TinyCircuits/TinyCircuits-Wireling-Temperature-Sensor-AST1021/cad/Wireling_TEMP_AST1021_REV2-DETAILED_DRAWING-PNG.png

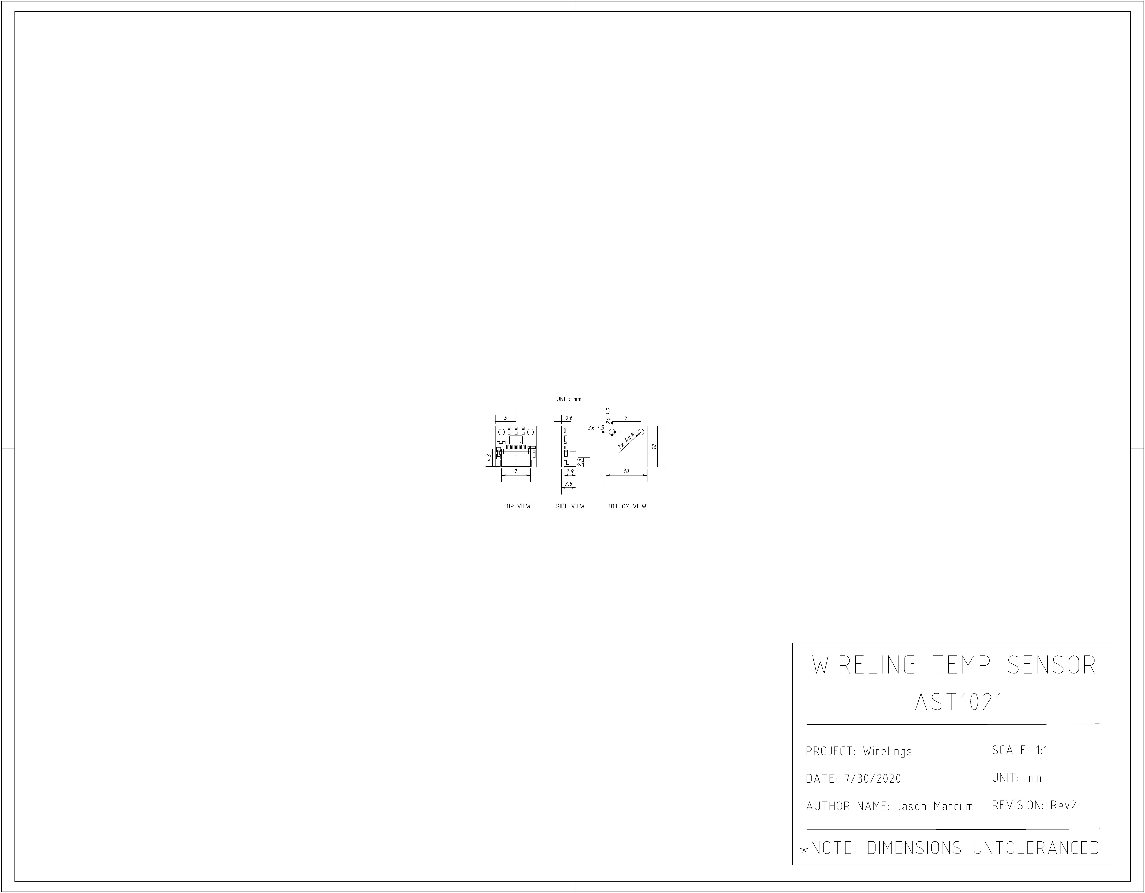
cad/Wireling_TEMP_AST1021_REV2-DETAILED_DRAWING-PNG.png
