TinyCircuits/TinyCircuits-Wireling-Temperature-Sensor-AST1021/images/AST1021-Product-Photo-01.png

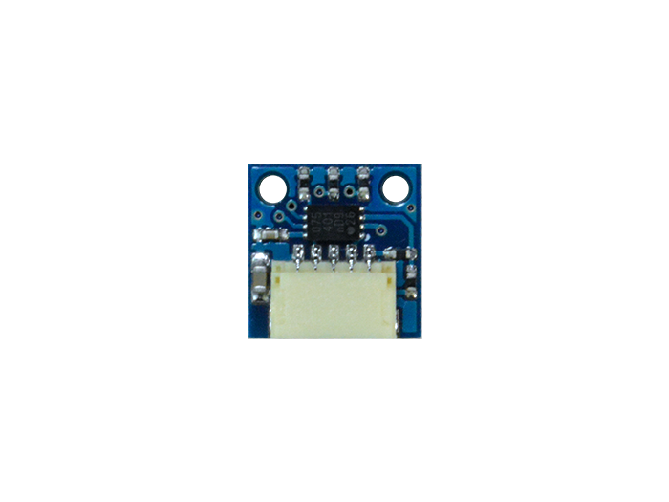
images/AST1021-Product-Photo-01.png
