TinyCircuits/TinyCircuits-Wireling-Temperature-Sensor-AST1021/images/AST1021-Tutorial-Image-03.gif

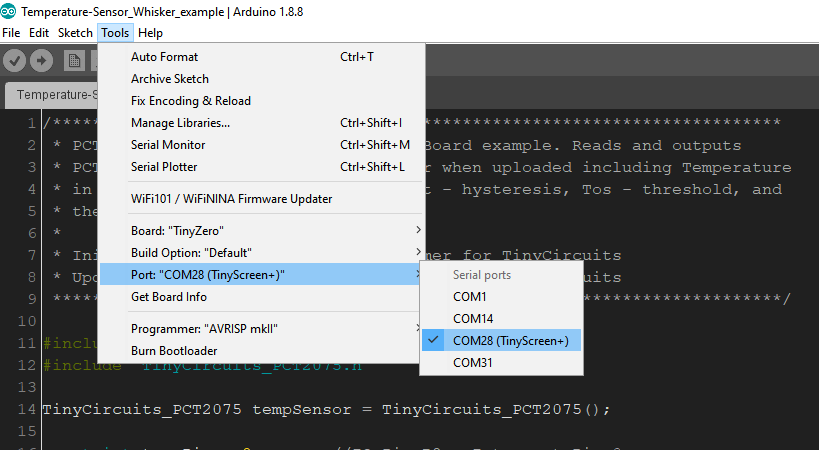
images/AST1021-Tutorial-Image-03.gif
